fenr1r/discomfort_index_meter/sch/KiCad_DI_Proj.kicad_sch

## KiCad design sch/KiCad_DI_Proj.kicad_sch (2025-12-06)

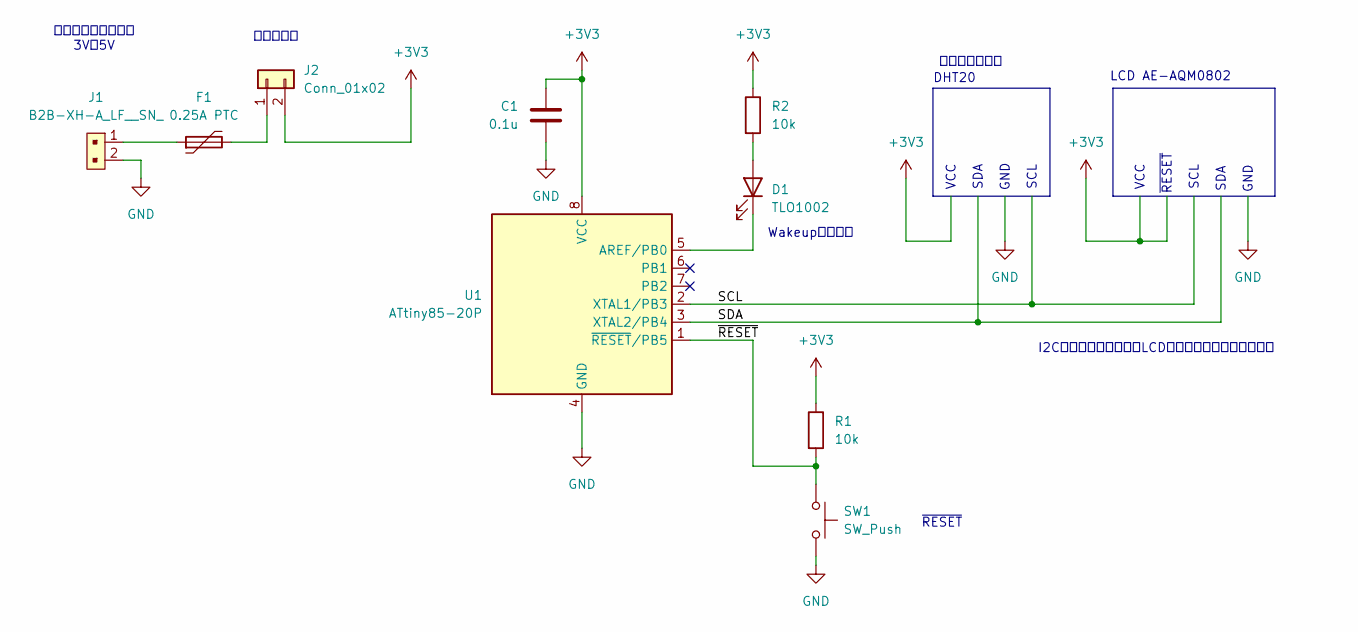
[picture p2: schematic KiCad_DI_Proj.kicad_sch]

Parts:
C1: 0.1u
D1: TLO1002
F1: 0.25A PTC
J1: B2B-XH-A_LF__SN_; PinHeader_1x2_P2.5mm_Drill1.1mm; MPN B2B-XH-A(LF)(SN); Digi-Key_PN 455-2247-ND
J2: Conn_01x02
R1, R2: 10k
SW1: SW_Push
U1: ATtiny85-20P; DIP-8_W7.62mm

Connections:
+3V3: C1.1, J2.2, R1.1, R2.1, U1.8 (VCC)
GND: C1.2, J1.2, SW1.2, U1.4 (GND)
unnamed: D1.1 (K), U1.5 (AREF/PB0)
unnamed: D1.2 (A), R2.2
unnamed: F1.1, J1.1
unnamed: F1.2, J2.1
SCL: U1.2 (XTAL1/PB3)
SDA: U1.3 (XTAL2/PB4)
~RESET: R1.2, SW1.1, U1.1 (~RESET/PB5)

Notes on the sheet:
電流測定用
Wakeup中に点灯
DHT20
SCL
~{RESET}
SDA
I2Cのプルアップ抵抗はLCDモジュール裏のものを使用
湿温度センサー
GND
LCD AE-AQM0802
VCC
電池スナップに接続 3V～5V
